Davidos1243/Audio-Power-Amplifier/Ltspice/project.asc

C1: cap; 1n
C2: cap; 2.2n
C3: cap; 220n
C4: cap; 120n
R1: res; 2k
R2: res; 0.5
R3: res; 10k
R4: res; 366.9
R5: res; 3.9k
R6: res; 3.9k
R7: res; 6.8k
R11: res; 1.8k
R16: res; 8
R17: res; 2k
R18: res; 100
U1: OPA132
U2: OPA132
U3: OPA132
U4: OPA132
U5: LM3886
V1: voltage; 36
V2: voltage; 36
V3: voltage; 12
V4: voltage; 12
V5: voltage; SINE(0 1 1k 0 0 0)
Named nets: 0, +Vin_P, +Vin, -Vin_P, -Vin
.tran 0 .02 .018 .001
.ac dec 10 1 100k
